Scottapotamas/stm32-camera/Firmware/stm32-camera/Src/app_hal/hal_gpio_types.h

/**
 * @file      hal_gpio_types.h
 *
 * @brief     Type declarations for GPIO use.
 *
 * @author    Marco Hess <marcoh@applidyne.com.au>
 *
 * @copyright (c) 2017 Applidyne Pty. Ltd. - All rights reserved.
*/

#ifndef HAL_GPIO_TYPES_H
#define HAL_GPIO_TYPES_H

#ifdef __cplusplus
extern "C" {
#endif

#include <stdbool.h>

#include "global.h"

/** Readability macros to remind us which is a HIGH level or LOW level */
#define GPIO_HIGH       true
#define GPIO_LOW        false

/** Map the pin number into a bit mask */
#define HAL_GPIO_PIN_MASK( pin_nr )   (1UL << ( pin_nr ))

/* ----- Types ------------------------------------------------------------- */

/** Operational mode for pins */

typedef enum
{
    MODE_INPUT = 0, /* Normal input */
    MODE_INPUT_PU, /* Input with PU */
    MODE_ANALOG,    /* Analog Mode  */
    MODE_OUT_PP,    /* Push-Pull Output */
    MODE_OUT_OD     /* Open drain Output */
} HalGpioMode_t;

/** Port Number */
typedef enum
{
    PORT_A = (0),
    PORT_B = (1),
    PORT_C = (2),
    PORT_D = (3),
    PORT_E = (4),
    PORT_F = (5),
    PORT_G = (6),
    PORT_H = (7),
	I2C_PLACEHOLDER
} HalGpioPortNr_t;

/** Pin Numbers */
typedef enum
{
    PIN_0,
    PIN_1,
    PIN_2,
    PIN_3,
    PIN_4,
    PIN_5,
    PIN_6,
    PIN_7,
    PIN_8,
    PIN_9,
    PIN_10,
    PIN_11,
    PIN_12,
    PIN_13,
    PIN_14,
    PIN_15,
} HalGpioPinNr_t;

typedef struct
{
    unsigned mode       : 3;      /* GPIO Mode (Input, Output Push Pull, etc. ) TODO work out analog pin mode requiring more bits*/
    unsigned port       : 4;      /* GPIO Port */
    unsigned pin        : 5;      /* Pin Number within port or i2C device */
    unsigned initial    : 1;      /* Initialisation level for outputs */
} HalGpioDef_t;

/* ----- End ---------------------------------------------------------------- */

#ifdef __cplusplus
}
#endif

#endif /* HAL_GPIO_TYPES_H */
