Scottapotamas/stm32-camera/Firmware/stm32-camera/Src/app_hal/hal_uart.h

/**
 * @file      hal_uart.h
 *
 * @brief     Low level interface to the UARTs.
 *
 * @author    Marco Hess <marcoh@applidyne.com.au>
 *
 * @copyright (c) 2017 Applidyne Pty. Ltd. - All rights reserved.
*/

#ifndef HAL_UART_H
#define HAL_UART_H

#ifdef __cplusplus
extern "C" {
#endif

/* ----- System Includes ---------------------------------------------------- */

#include <stdint.h>
#include <stdbool.h>

/* ----- Local Includes ----------------------------------------------------- */

#include "global.h"

/* ----- Types ------------------------------------------------------------- */

typedef enum
{
    HAL_UART_PORT_MAIN,
    HAL_UART_NUM_PORTS
} HalUartPort_t;

typedef void (*HalUartRxCallback_t)( HalUartPort_t port, uint8_t c );

/* -------------------------------------------------------------------------- */
/* --- UART INTERFACE                                                     --- */
/* -------------------------------------------------------------------------- */

/** Initialise the UARTs */

PUBLIC void
hal_uart_init( HalUartPort_t port );

/* -------------------------------------------------------------------------- */

/* Reset the UART (for after clock speed change) */

PUBLIC void
hal_uart_reinit( HalUartPort_t port );

/* -------------------------------------------------------------------------- */

/** Activate the UART peripheral */

PUBLIC void
hal_uart_activate( HalUartPort_t port );

/* -------------------------------------------------------------------------- */

/** Deactivate the UART peripheral */

PUBLIC void
hal_uart_deactivate( HalUartPort_t port );

/* -------------------------------------------------------------------------- */

/** Configure the UART baudrate */

PUBLIC void
hal_uart_baudrate( HalUartPort_t port, uint32_t baudrate );

/* -------------------------------------------------------------------------- */

/* Non-blocking send for a single character to the UART tx FIFO queue.
 * Returns true when successful. false when queue was full.
 */

PUBLIC bool
hal_uart_put( HalUartPort_t port, uint8_t c );

/* -------------------------------------------------------------------------- */

/** Wait until FIFO cleared. */

PUBLIC void
hal_uart_flush( HalUartPort_t port );

/* -------------------------------------------------------------------------- */

/* Blocking send for a single character to the UART tx FIFO queue.
 * Can still return unsuccessfully when timing out.
 * Returns true when successful. false when queue was full.
 */

PUBLIC bool
hal_uart_put_blocking( HalUartPort_t port, uint8_t c );

/* -------------------------------------------------------------------------- */

/* Non-blocking send for a number of characters to the UART tx FIFO queue.
 * Returns true when successful. false when queue was full.
 */

PUBLIC uint32_t
hal_uart_write( HalUartPort_t port, const uint8_t * data, uint32_t length );

/* -------------------------------------------------------------------------- */

/* Register a receive handler.
 * Called directly from UART ISR. When this is used, there is no buffering
 * available and the hal_uart_get is no longer functional.
 */

PUBLIC void
hal_uart_set_rx_handler( HalUartPort_t port, HalUartRxCallback_t rxFunc );

/* -------------------------------------------------------------------------- */

/* Returns number of available characters in the RX FIFO queue. */

PUBLIC uint32_t
hal_uart_rx_data_available( HalUartPort_t port );

/* -------------------------------------------------------------------------- */

/* Retrieve a single byte from the rx FIFO queue.
 * Returns 0 when no data is available or when rx callback is in use.
 */

PUBLIC uint8_t
hal_uart_rx_get( HalUartPort_t port );

/* -------------------------------------------------------------------------- */

/* Retrieve a number of bytes from the rx FIFO queue up to
 * buffer length. Returns the number of bytes actually read.
 */

PUBLIC uint32_t
hal_uart_read( HalUartPort_t port, uint8_t * buffer, uint32_t bufferlen );

/* -------------------------------------------------------------------------- */

/* Blocking printf to the UART.
 * To be used within assert and fault handlers to print fault
 * information.
 */

PUBLIC void
hal_uart_printf_direct( HalUartPort_t port, const char * format, ... );

/* ----- End ---------------------------------------------------------------- */

#ifdef __cplusplus
}
#endif

#endif /* HAL_UART_H */
