Scottapotamas/stm32-camera/Firmware/stm32-camera/Src/app_state_machines/app_events.h

/**
 * @file    app_events.h
 *
 * @brief   Application Level Custom Event Structures.
 *
 * @author  Marco Hess <marcoh@applidyne.com.au>
 *
 * @copyright (c) 2013-2015 Applidyne Pty. Ltd. - All rights reserved.
 */

#ifndef APP_EVENTS_H
#define APP_EVENTS_H

#ifdef __cplusplus
extern "C" {
#endif

/* ----- System Includes ---------------------------------------------------- */

#include <stdint.h>
#include <stdbool.h>
#include <time.h>

/* ----- Local Includes ----------------------------------------------------- */

#include "global.h"
#include "app_config.h"
#include "state_task.h"
#include "state_event.h"
#include "button.h"
#include "hal_i2c.h"
#include "auxiliary.h"
#include "hal_uart.h"
#include "ff.h"
#include "auxiliary.h"
#include "log.h"

/* -------------------------------------------------------------------------- */

/** Internal report of button event */
typedef struct ButtonEvent__
{
    StateEvent        super;             /**< Encapsulated event reference */
    ButtonId_t        id;                /**< ID number of button event */
    ButtonPressType_t press_type;        /**< Type of button event */
} ButtonEvent;

/** Report detected button presses */
typedef struct ButtonPressedEvent__
{
    StateEvent    super;             /**< Encapsulated event reference */
    ButtonId_t    id;                /**< ID number of button event */
} ButtonPressedEvent;

/* -------------------------------------------------------------------------- */

/** Camera Capture Cmd Event Structures */
typedef struct CameraCaptureEvent__
{
    StateEvent          super;          /**< Encapsulated event reference */
    uint16_t            trigger_delay_ms;   /**< Time in ms to wait before taking picture */
} CameraCaptureEvent;

/* -------------------------------------------------------------------------- */

/** Camera Save Event Structures */
typedef struct CameraSaveEvent__
{
    StateEvent      super;              /**< Encapsulated event reference */
    uint8_t         percent_saved;      /**< Percentage of image saved */
} CameraSaveEvent;

/* -------------------------------------------------------------------------- */

/** Report changes in auxillary mode */
typedef struct AuxiliaryModeEvent__
{
    StateEvent       super;          /**< Encapsulated event reference */
    AuxiliaryPort_t  port;           /**< Aux port for mode switch */
    AuxiliaryMode_t  mode;           /**< Aux mode to switch to */
} AuxiliaryModeEvent;

/* -------------------------------------------------------------------------- */

/** Log Buffer Event - Generated when a log message occurs */
typedef struct LogBufferEvent__
{
    StateEvent      super;              /**< Encapsulated event reference */
    LOG_LEVEL       level;              /**< Log Message Level */
    uint32_t        used;               /**< Log buffer space used */
    uint32_t        percent;            /**< Log Buffer percentage used */
} LogBufferEvent;

/* -------------------------------------------------------------------------- */

/** Report changes in terminal mode */
typedef struct TerminalModeEvent__
{
    StateEvent       super;          /**< Encapsulated event reference */
    HalUartPort_t	 port;           /**< terminal port for mode switch */
    //TODO use a mode object here to act as baud rate allowing for event calls on baud change.
} TerminalModeEvent;

/* -------------------------------------------------------------------------- */

typedef struct TerminalCharEvent__
{
    StateEvent    super;
    uint8_t       ch;
} TerminalCharEvent;

/* -------------------------------------------------------------------------- */

/** Report detected button presses */
typedef struct KeyboardEvent__
{
    StateEvent super;             /**< Encapsulated event reference */
    char       key;
} KeyboardEvent;

/* -------------------------------------------------------------------------- */

/** File System Status Event Structures */
typedef struct FileSystemRequestEvent__
{
    StateEvent super;             /**< Encapsulated event reference */
    StateTask  *task;             /**< Task pointer making the request.
                                       Should not be more than 1 per task */
} FileSystemRequestEvent;

/* -------------------------------------------------------------------------- */

/** File System Status Event Structures */
typedef struct FileSystemStatusEvent__
{
    StateEvent super;             /**< Encapsulated event reference */
    FRESULT    f_result;          /**< FatFS FRESULT of mount/unmount */
    uint8_t    number_of_mounts;  /**< Number of tasks with an open mount */
    uint32_t   space_total_KiB;   /**< Total KiB for disk */
    uint32_t   space_free_KiB;    /**< Free KiB on disk */
} FileSystemStatusEvent;

/* ----- End ---------------------------------------------------------------- */

#ifdef __cplusplus
}
#endif

#endif /* APP_EVENTS_H */
