Scottapotamas/stm32-camera/Firmware/stm32-camera/Src/app_state_machines/app_task_terminal.c

/**
 * @file    app_task_terminal.c
 *
 * @ingroup tasks
 *
 * @brief   blah
 *
 *
 * @copyright (c) 2015 Applidyne Pty. Ltd. - All rights reserved.
 */

/* ----- System Includes ---------------------------------------------------- */

#include <ctype.h>
#include <string.h>
#include <event_subscribe.h>

/* ----- Local Includes ----------------------------------------------------- */

#include "global.h"
#include "qassert.h"
#include "app_config.h"
#include "app_tasks.h"
#include "app_task_ids.h"
#include "app_times.h"
#include "app_signals.h"
#include "app_events.h"
#include "app_version.h"
#include "hal_systick.h"

#include "app_task_terminal.h"
#include "app_task_terminal_private.h"
#include "commands.h"
#include "log.h"
#include "config.h"

/* -------------------------------------------------------------------------- */

//DEFINE_THIS_FILE; /* Used for ASSERT checks to define __FILE__ only once */

/* ----------------------- Public Functions --------------------------------- */

PUBLIC StateTask *
appTaskTerminalCreate( AppTaskTerminal   *me,
                        StateEvent         *eventQueueData[ ],
                        const uint8_t      eventQueueSize,
						HalUartPort_t      instance )
{
    /* Clear all task data */
    memset( me, 0, sizeof(AppTaskTerminal) );

    /* Initialise State Machine structures */
    AppTaskTerminalConstructor( me );

    /* Which uart are we talking about */
    me->instance = instance;

    /* Initialise State Machine Task */
    return stateTaskCreate( (StateTask*)me,
                            eventQueueData,
                            eventQueueSize,
                            0,
                            0 );
}

/* ----- Private Functions -------------------------------------------------- */

/* State Machine Construction */
PRIVATE void AppTaskTerminalConstructor( AppTaskTerminal *me )
{
    stateTaskCtor( &me->super, (State)&AppTaskTerminal_initial );
}

/* -------------------------------------------------------------------------- */

/*  State Machine Initial State */
PRIVATE void AppTaskTerminal_initial( AppTaskTerminal *me,
                                       const StateEvent *e __attribute__((__unused__)) )
{
    eventSubscribe( (StateTask*)me, TERMINAL_MODE_SIGNAL );
    STATE_INIT( &AppTaskTerminal_main );
}

/* -------------------------------------------------------------------------- */

/* State Machine Initial State */
PRIVATE STATE
AppTaskTerminal_main( AppTaskTerminal *me,
                       const StateEvent *e )
{
    switch( e->signal )
    {
        case STATE_ENTRY_SIGNAL:

        	cmd_init( &me->monitor, commands );

        	//configure the uart
            hal_uart_init( me->instance );
            hal_uart_baudrate( me->instance, config_terminal_baudrate( me->instance ) );
            hal_uart_set_rx_handler( me->instance, AppTaskTerminal_rx_callback );

            //configure the terminal interface
            cmd_set_output_put( &me->monitor, AppTaskTerminal_tx_put );
            cmd_set_output_flush( &me->monitor,  AppTaskTerminal_tx_flush );
            cmd_set_echo( &me->monitor, true );

            //Logging system can use this monitor as the output.
            command_log_set_mask( &me->monitor, 0xFFFF, LOG_MASK_ALL );

            //print board info to terminal
            cmd_printf( &me->monitor,
                        "\r\n*** %s - %s (%s) %s ***\r\n\r\n",
                        ProgramName,
                        ProgramBuildInfo,
                        ProgramBuildDate,
                        ProgramBuildType );
            cmd_input_func( &me->monitor, '\r' );

            return 0;

        case TERMINAL_INPUT_CHAR_SIGNAL:
            cmd_input_func( &me->monitor, ((TerminalCharEvent*)e)->ch );
            //no break

        case STATE_STEP1_SIGNAL:
            me->monitor.flags.cmdDone = cmd_main_loop( &me->monitor );
            if( !me->monitor.flags.cmdDone )
            {
                /* Repeat until done */
                stateTaskPostReservedEvent( STATE_STEP1_SIGNAL );
            }
            return 0;
    }
    return (STATE)hsmTop;
}

/* -------------------------------------------------------------------------- */

//TODO write state machine to handle changing baud rate

/* ----- Callback Helper Functions ------------------------------------------ */

PRIVATE bool
AppTaskTerminal_tx_put( uint8_t c )
{
    return hal_uart_put( HAL_UART_PORT_MAIN, c );
}

/* -------------------------------------------------------------------------- */

PRIVATE void
AppTaskTerminal_tx_flush( void )
{
    hal_uart_flush( HAL_UART_PORT_MAIN );
}

/* -------------------------------------------------------------------------- */

/* Simple callback for received characters */
PRIVATE void
AppTaskTerminal_rx_callback( HalUartPort_t port, uint8_t c )
{
    if( port == HAL_UART_PORT_MAIN )
    {
        TerminalCharEvent *e = EVENT_NEW( TerminalCharEvent, TERMINAL_INPUT_CHAR_SIGNAL );

        // Failure of EVENT_NEW allocate results in a corrupted input message
        if( e )
        {
            e->ch = c;
            if( port == HAL_UART_PORT_MAIN )
            {
                stateTaskPostFIFO( app_task_by_id( TASK_TERMINAL ),
                                   (StateEvent*)e );
            }

        }
    }
    else
    {
    	//handle other uart ports here if future boards need them
    }
}

/* ----- End ---------------------------------------------------------------- */
