Scottapotamas/stm32-camera/Firmware/stm32-camera/Src/app_hal/hal_solenoid.c

/**
 * @file      hal_solenoid.c
 *
 * @brief     Low level interface to the solenoid drive "H-Bridge".
 *
*/

/* ----- System Includes ---------------------------------------------------- */

/* ----- Local Includes ----------------------------------------------------- */

#include "hal_solenoid.h"
#include "stm32f4xx_hal.h"


PUBLIC void
hal_solenoid_init( )
{
    //TODO init solenoid drive
}

/* -------------------------------------------------------------------------- */

PUBLIC void
hal_solenoid_off( )
{
    //write all pins as 'off'
    HAL_GPIO_WritePin(GPIOE, GPIO_PIN_7|GPIO_PIN_8|GPIO_PIN_9|GPIO_PIN_10, GPIO_PIN_RESET);
    HAL_GPIO_WritePin(GPIOE, GPIO_PIN_11|GPIO_PIN_12|GPIO_PIN_13|GPIO_PIN_14, GPIO_PIN_RESET);

    //turn all pins to an input or analog "passive" state for "off"
    GPIO_InitTypeDef GPIO_InitStruct;

    GPIO_InitStruct.Pin = GPIO_PIN_7|GPIO_PIN_8|GPIO_PIN_9|GPIO_PIN_10|
                          GPIO_PIN_11|GPIO_PIN_12|GPIO_PIN_13|GPIO_PIN_14;
    GPIO_InitStruct.Mode = GPIO_MODE_ANALOG;    //save power by setting as analog
    GPIO_InitStruct.Pull = GPIO_NOPULL;
    GPIO_InitStruct.Speed = GPIO_SPEED_FREQ_LOW;

    HAL_GPIO_Init(GPIOE, &GPIO_InitStruct);
}

/* -------------------------------------------------------------------------- */

PUBLIC void
hal_solenoid_activate( bool polarity )
{
    //port setup for pins
    GPIO_InitTypeDef GPIO_InitStruct;

    GPIO_InitStruct.Pin = GPIO_PIN_7|GPIO_PIN_8|GPIO_PIN_9|GPIO_PIN_10|
                          GPIO_PIN_11|GPIO_PIN_12|GPIO_PIN_13|GPIO_PIN_14;
    GPIO_InitStruct.Mode = GPIO_MODE_OUTPUT_PP;    //configure push pull
    GPIO_InitStruct.Pull = GPIO_NOPULL;
    GPIO_InitStruct.Speed = GPIO_SPEED_FREQ_LOW;

    HAL_GPIO_Init(GPIOE, &GPIO_InitStruct);

    //write all pins as 'off'
    HAL_GPIO_WritePin(GPIOE, GPIO_PIN_7|GPIO_PIN_8|GPIO_PIN_9|GPIO_PIN_10, GPIO_PIN_RESET);
    HAL_GPIO_WritePin(GPIOE, GPIO_PIN_11|GPIO_PIN_12|GPIO_PIN_13|GPIO_PIN_14, GPIO_PIN_RESET);

    hal_delay_ms(1);    //todo don't delay in solenoid like this

    //half the port has polarity, the other half has !polarity to set them half on and half off
    HAL_GPIO_WritePin(GPIOE, GPIO_PIN_7|GPIO_PIN_8|GPIO_PIN_9|GPIO_PIN_10, polarity);
    HAL_GPIO_WritePin(GPIOE, GPIO_PIN_11|GPIO_PIN_12|GPIO_PIN_13|GPIO_PIN_14, !polarity);

}


/* ----- End ---------------------------------------------------------------- */
