Scottapotamas/stm32-camera/Firmware/stm32-camera/Src/app_hal/hal_uuid.h

/**
 * @file      hal_uuid.c
 *
 * @brief     A simple header for reading the STM32 device UUID
 *            Tested with STM32F4 and STM32F0 families
 *
 * @author    Uli Koehler
 *            Published on http://techoverflow.net
 *
 * @licence   Licensed under CC0 (public domain):
 *            https://creativecommons.org/publicdomain/zero/1.0/
 */

#ifndef HAL_UUID_H
#define HAL_UUID_H

#include <stdint.h>

/**
 * The STM32 factory-programmed UUID memory.
 * Three values of 32 bits each starting at this address
 * Use like this: STM32_UUID[0], STM32_UUID[1], STM32_UUID[2]
 */
#define HAL_UUID ((uint32_t *)0x1FFF7A10)

#endif /* HAL_UUID_H */
 
