Scottapotamas/stm32-camera/Firmware/stm32-camera/Src/app_state_machines/app_background.c

/**
 * @file      app_background.c
 *
 * @brief     Application main loop background processes
 *
 * @author    Marco Hess <marcoh@applidyne.com.au>
 *
 * @copyright (c) 2017 Applidyne Pty. Ltd. - All rights reserved.
 */

/* ----- System Includes ---------------------------------------------------- */


/* ----- Local Includes ----------------------------------------------------- */

#include "app_background.h"
#include "event_subscribe.h"
#include "app_signals.h"
#include "button.h"
#include "hal_button.h"
#include "timer.h"

/* -------------------------------------------------------------------------- */

PRIVATE timer_t button_timer = 0;

/* -------------------------------------------------------------------------- */

PUBLIC void
app_background_init( void )
{
    timerStart( &button_timer, 50 );

}

/* -------------------------------------------------------------------------- */

PUBLIC void
app_background( void )
{
    if( timerIsExpired( &button_timer ) )
    {
        timerStart( &button_timer, 50 );
    }

    /* Scan buttons */
    button_process();

}

/* ----- End ---------------------------------------------------------------- */
