Scottapotamas/stm32-camera/Firmware/stm32-camera/Src/app_state_machines/app_background.h

/**
 * @file      app_background.h
 *
 * @brief     Application main loop background processes
 *
 * @author    Marco Hess <marcoh@applidyne.com.au>
 *
 * @copyright (c) 2017 Applidyne Pty. Ltd. - All rights reserved.
 */

#ifndef APP_BACKGROUND_H
#define APP_BACKGROUND_H

#ifdef __cplusplus
extern "C" {
#endif

/* ----- System Includes ---------------------------------------------------- */

/* ----- Local Includes ----------------------------------------------------- */

#include "global.h"

/* ----- Defines ------------------------------------------------------------ */

/* ----- Public Functions --------------------------------------------------- */

/** Startup initialisation for background processes in the main loop */

PUBLIC void
app_background_init( void );

/* -------------------------------------------------------------------------- */

/** Background processes that are handled in the main loop */

PUBLIC void
app_background( void );

/* ----- End ------------------------------~--------------------------------- */

#ifdef    __cplusplus
}
#endif
#endif /* APP_BACKGROUND_H */
