Scottapotamas/stm32-camera/Firmware/stm32-camera/Src/app_utility/eunity.c

/* =========================================================================
    eUnity Project - A Test Framework for C
    Copyright (c) 2007-14 Mike Karlesky, Mark VanderVoord, Greg Williams
    [Released under MIT License. Please refer to license.txt for details]
============================================================================ */

#include "eunity.h"
#include <stddef.h>

/* If omitted from header, declare overrideable prototypes here so they're ready for use */
#ifdef EUNITY_OMIT_OUTPUT_CHAR_HEADER_DECLARATION
void EUNITY_OUTPUT_CHAR(int);
#endif

/* Helpful macros for us to use here */
#define EUNITY_FAIL_AND_BAIL   { eUnity.CurrentTestFailed  = 1; longjmp(eUnity.AbortFrame, 1); }
#define EUNITY_IGNORE_AND_BAIL { eUnity.CurrentTestIgnored = 1; longjmp(eUnity.AbortFrame, 1); }

/* return prematurely if we are already in failure or ignore state */
#define EUNITY_SKIP_EXECUTION  { if ((eUnity.CurrentTestFailed != 0) || (eUnity.CurrentTestIgnored != 0)) {return;} }

struct _eUnity eUnity;

static const char eUnityStrOk[]                     = "OK";
static const char eUnityStrPass[]                   = "PASS";
static const char eUnityStrFail[]                   = "FAIL";
static const char eUnityStrIgnore[]                 = "IGNORE";
static const char eUnityStrNull[]                   = "NULL";
static const char eUnityStrSpacer[]                 = ". ";
static const char eUnityStrExpected[]               = " Expected ";
static const char eUnityStrWas[]                    = " Was ";
static const char eUnityStrElement[]                = " Element ";
static const char eUnityStrByte[]                   = " Byte ";
static const char eUnityStrMemory[]                 = " Memory Mismatch.";
static const char eUnityStrDelta[]                  = " Values Not Within Delta ";
static const char eUnityStrPointless[]              = " You Asked Me To Compare Nothing, Which Was Pointless.";
static const char eUnityStrNullPointerForExpected[] = " Expected pointer to be NULL";
static const char eUnityStrNullPointerForActual[]   = " Actual pointer was NULL";
static const char eUnityStrNot[]                    = "Not ";
static const char eUnityStrInf[]                    = "Infinity";
static const char eUnityStrNegInf[]                 = "Negative Infinity";
static const char eUnityStrNaN[]                    = "NaN";
static const char eUnityStrDet[]                    = "Determinate";
static const char eUnityStrInvalidFloatTrait[]      = "Invalid Float Trait";
const char eUnityStrErrFloat[]                      = "Unity Floating Point Disabled";
const char eUnityStrErrDouble[]                     = "Unity Double Precision Disabled";
const char eUnityStrErr64[]                         = "Unity 64-bit Support Disabled";
static const char eUnityStrBreaker[]                = "-----------------------";
static const char eUnityStrResultsTests[]           = " Tests ";
static const char eUnityStrResultsFailures[]        = " Failures ";
static const char eUnityStrResultsIgnored[]         = " Ignored ";
static const char eUnityStrDetail1Name[]            = EUNITY_DETAIL1_NAME " ";
static const char eUnityStrDetail2Name[]            = " " EUNITY_DETAIL2_NAME " ";

#ifdef EUNITY_FLOAT_NEEDS_ZERO
/* Dividing by these constants produces +/- infinity.
 * The rationale is given in eUnityAssertFloatIsInf's body. */
static const _UF f_zero = 0.0f;
#endif

/* compiler-generic print formatting masks */
static const _U_UINT eUnitySizeMask[] =
{
    255u,         /* 0xFF */
    65535u,       /* 0xFFFF */
    65535u,
    4294967295u,  /* 0xFFFFFFFF */
    4294967295u,
    4294967295u,
    4294967295u
#ifdef EUNITY_SUPPORT_64
    ,0xFFFFFFFFFFFFFFFF
#endif
};

/*-----------------------------------------------
 * Pretty Printers & Test Result Output Handlers
 *-----------------------------------------------*/

void eUnityPrint(const char* string)
{
    const char* pch = string;

    if (pch != NULL)
    {
        while (*pch)
        {
            /* printable characters plus CR & LF are printed */
            if ((*pch <= 126) && (*pch >= 32))
            {
                EUNITY_OUTPUT_CHAR(*pch);
            }
            /* write escaped carriage returns */
            else if (*pch == 13)
            {
                EUNITY_OUTPUT_CHAR('\\');
                EUNITY_OUTPUT_CHAR('r');
            }
            /* write escaped line feeds */
            else if (*pch == 10)
            {
                EUNITY_OUTPUT_CHAR('\\');
                EUNITY_OUTPUT_CHAR('n');
            }
            /* unprintable characters are shown as codes */
            else
            {
                EUNITY_OUTPUT_CHAR('\\');
                eUnityPrintNumberHex((_U_UINT)*pch, 2);
            }
            pch++;
        }
    }
}

void eUnityPrintLen(const char* string, const _UU32 length);
void eUnityPrintLen(const char* string, const _UU32 length)
{
    const char* pch = string;

    if (pch != NULL)
    {
        while (*pch && (_UU32)(pch - string) < length)
        {
            /* printable characters plus CR & LF are printed */
            if ((*pch <= 126) && (*pch >= 32))
            {
                EUNITY_OUTPUT_CHAR(*pch);
            }
            /* write escaped carriage returns */
            else if (*pch == 13)
            {
                EUNITY_OUTPUT_CHAR('\\');
                EUNITY_OUTPUT_CHAR('r');
            }
            /* write escaped line feeds */
            else if (*pch == 10)
            {
                EUNITY_OUTPUT_CHAR('\\');
                EUNITY_OUTPUT_CHAR('n');
            }
            /* unprintable characters are shown as codes */
            else
            {
                EUNITY_OUTPUT_CHAR('\\');
                eUnityPrintNumberHex((_U_UINT)*pch, 2);
            }
            pch++;
        }
    }
}

/*-----------------------------------------------*/
void eUnityPrintNumberByStyle(const _U_SINT number, const EUNITY_DISPLAY_STYLE_T style)
{
    if ((style & EUNITY_DISPLAY_RANGE_INT) == EUNITY_DISPLAY_RANGE_INT)
    {
        eUnityPrintNumber(number);
    }
    else if ((style & EUNITY_DISPLAY_RANGE_UINT) == EUNITY_DISPLAY_RANGE_UINT)
    {
        eUnityPrintNumberUnsigned(  (_U_UINT)number  &  eUnitySizeMask[((_U_UINT)style & (_U_UINT)0x0F) - 1]  );
    }
    else
    {
        eUnityPrintNumberHex((_U_UINT)number, (char)((style & 0x000F) << 1));
    }
}

/*-----------------------------------------------*/
void eUnityPrintNumber(const _U_SINT number_to_print)
{
    _U_UINT number = (_U_UINT)number_to_print;

    if (number_to_print < 0)
    {
        /* A negative number, including MIN negative */
        EUNITY_OUTPUT_CHAR('-');
        number = (_U_UINT)(-number_to_print);
    }
    eUnityPrintNumberUnsigned(number);
}

/*-----------------------------------------------
 * basically do an itoa using as little ram as possible */
void eUnityPrintNumberUnsigned(const _U_UINT number)
{
    _U_UINT divisor = 1;

    /* figure out initial divisor */
    while (number / divisor > 9)
    {
        divisor *= 10;
    }

    /* now mod and print, then divide divisor */
    do
    {
        EUNITY_OUTPUT_CHAR((char)('0' + (number / divisor % 10)));
        divisor /= 10;
    }
    while (divisor > 0);
}

/*-----------------------------------------------*/
void eUnityPrintNumberHex(const _U_UINT number, const char nibbles_to_print)
{
    _U_UINT nibble;
    char nibbles = nibbles_to_print;
    EUNITY_OUTPUT_CHAR('0');
    EUNITY_OUTPUT_CHAR('x');

    while (nibbles > 0)
    {
        nibble = (number >> (--nibbles << 2)) & 0x0000000F;
        if (nibble <= 9)
        {
            EUNITY_OUTPUT_CHAR((char)('0' + nibble));
        }
        else
        {
            EUNITY_OUTPUT_CHAR((char)('A' - 10 + nibble));
        }
    }
}

/*-----------------------------------------------*/
void eUnityPrintMask(const _U_UINT mask, const _U_UINT number)
{
    _U_UINT current_bit = (_U_UINT)1 << (EUNITY_INT_WIDTH - 1);
    _US32 i;

    for (i = 0; i < EUNITY_INT_WIDTH; i++)
    {
        if (current_bit & mask)
        {
            if (current_bit & number)
            {
                EUNITY_OUTPUT_CHAR('1');
            }
            else
            {
                EUNITY_OUTPUT_CHAR('0');
            }
        }
        else
        {
            EUNITY_OUTPUT_CHAR('X');
        }
        current_bit = current_bit >> 1;
    }
}

/*-----------------------------------------------*/
#ifdef EUNITY_FLOAT_VERBOSE
#include <stdio.h>

#ifndef EUNITY_VERBOSE_NUMBER_MAX_LENGTH
# ifdef EUNITY_DOUBLE_VERBOSE
#  define EUNITY_VERBOSE_NUMBER_MAX_LENGTH 317
# else
#  define EUNITY_VERBOSE_NUMBER_MAX_LENGTH 47
# endif
#endif

void eUnityPrintFloat(_UF number)
{
    char TempBuffer[EUNITY_VERBOSE_NUMBER_MAX_LENGTH + 1];
    snprintf(TempBuffer, sizeof(TempBuffer), "%.6f", number);
    eUnityPrint(TempBuffer);
}
#endif

/*-----------------------------------------------*/

void eUnityPrintFail(void);
void eUnityPrintFail(void)
{
    eUnityPrint(eUnityStrFail);
}

void eUnityPrintOk(void);
void eUnityPrintOk(void)
{
    eUnityPrint(eUnityStrOk);
}

/*-----------------------------------------------*/
static void eUnityTestResultsBegin(const char* file, const EUNITY_LINE_TYPE line);
static void eUnityTestResultsBegin(const char* file, const EUNITY_LINE_TYPE line)
{
#ifndef EUNITY_FIXTURES
    eUnityPrint(file);
    EUNITY_OUTPUT_CHAR(':');
    eUnityPrintNumber((_U_SINT)line);
    EUNITY_OUTPUT_CHAR(':');
    eUnityPrint(eUnity.CurrentTestName);
    EUNITY_OUTPUT_CHAR(':');
#else
    EUNITY_UNUSED(file);
    EUNITY_UNUSED(line);
#endif
}

/*-----------------------------------------------*/
static void eUnityTestResultsFailBegin(const EUNITY_LINE_TYPE line);
static void eUnityTestResultsFailBegin(const EUNITY_LINE_TYPE line)
{
#ifndef EUNITY_FIXTURES
    eUnityTestResultsBegin(eUnity.TestFile, line);
#else
    EUNITY_UNUSED(line);
#endif
    eUnityPrint(eUnityStrFail);
    EUNITY_OUTPUT_CHAR(':');
}

/*-----------------------------------------------*/
void eUnityConcludeTest(void)
{
    if (eUnity.CurrentTestIgnored)
    {
        eUnity.TestIgnores++;
    }
    else if (!eUnity.CurrentTestFailed)
    {
        eUnityTestResultsBegin(eUnity.TestFile, eUnity.CurrentTestLineNumber);
        eUnityPrint(eUnityStrPass);
    }
    else
    {
        eUnity.TestFailures++;
    }

    eUnity.CurrentTestFailed = 0;
    eUnity.CurrentTestIgnored = 0;
    EUNITY_PRINT_EOL();
    EUNITY_FLUSH_CALL();
}

/*-----------------------------------------------*/
static void eUnityAddMsgIfSpecified(const char* msg);
static void eUnityAddMsgIfSpecified(const char* msg)
{
    if (msg)
    {
        eUnityPrint(eUnityStrSpacer);
#ifndef EUNITY_EXCLUDE_DETAILS
        if (eUnity.CurrentDetail1)
        {
            eUnityPrint(eUnityStrDetail1Name);
            eUnityPrint(eUnity.CurrentDetail1);
            if (eUnity.CurrentDetail2)
            {
                eUnityPrint(eUnityStrDetail2Name);
                eUnityPrint(eUnity.CurrentDetail2);
            }
            eUnityPrint(eUnityStrSpacer);
        }
#endif
        eUnityPrint(msg);
    }
}

/*-----------------------------------------------*/
static void eUnityPrintExpectedAndActualStrings(const char* expected, const char* actual);
static void eUnityPrintExpectedAndActualStrings(const char* expected, const char* actual)
{
    eUnityPrint(eUnityStrExpected);
    if (expected != NULL)
    {
        EUNITY_OUTPUT_CHAR('\'');
        eUnityPrint(expected);
        EUNITY_OUTPUT_CHAR('\'');
    }
    else
    {
      eUnityPrint(eUnityStrNull);
    }
    eUnityPrint(eUnityStrWas);
    if (actual != NULL)
    {
        EUNITY_OUTPUT_CHAR('\'');
        eUnityPrint(actual);
        EUNITY_OUTPUT_CHAR('\'');
    }
    else
    {
      eUnityPrint(eUnityStrNull);
    }
}

/*-----------------------------------------------*/
static void eUnityPrintExpectedAndActualStringsLen(const char* expected, const char* actual, const _UU32 length)
{
    eUnityPrint(eUnityStrExpected);
    if (expected != NULL)
    {
        EUNITY_OUTPUT_CHAR('\'');
        eUnityPrintLen(expected, length);
        EUNITY_OUTPUT_CHAR('\'');
    }
    else
    {
      eUnityPrint(eUnityStrNull);
    }
    eUnityPrint(eUnityStrWas);
    if (actual != NULL)
    {
        EUNITY_OUTPUT_CHAR('\'');
        eUnityPrintLen(actual, length);
        EUNITY_OUTPUT_CHAR('\'');
    }
    else
    {
      eUnityPrint(eUnityStrNull);
    }
}



/*-----------------------------------------------
 * Assertion & Control Helpers
 *-----------------------------------------------*/

static int eUnityCheckArraysForNull(EUNITY_INTERNAL_PTR expected, EUNITY_INTERNAL_PTR actual, const EUNITY_LINE_TYPE lineNumber, const char* msg)
{
    /* return true if they are both NULL */
    if ((expected == NULL) && (actual == NULL))
        return 1;

    /* throw error if just expected is NULL */
    if (expected == NULL)
    {
        eUnityTestResultsFailBegin(lineNumber);
        eUnityPrint(eUnityStrNullPointerForExpected);
        eUnityAddMsgIfSpecified(msg);
        EUNITY_FAIL_AND_BAIL;
    }

    /* throw error if just actual is NULL */
    if (actual == NULL)
    {
        eUnityTestResultsFailBegin(lineNumber);
        eUnityPrint(eUnityStrNullPointerForActual);
        eUnityAddMsgIfSpecified(msg);
        EUNITY_FAIL_AND_BAIL;
    }

    /* return false if neither is NULL */
    return 0;
}

/*-----------------------------------------------
 * Assertion Functions
 *-----------------------------------------------*/

void eUnityAssertBits(const _U_SINT mask,
                     const _U_SINT expected,
                     const _U_SINT actual,
                     const char* msg,
                     const EUNITY_LINE_TYPE lineNumber)
{
    EUNITY_SKIP_EXECUTION;

    if ((mask & expected) != (mask & actual))
    {
        eUnityTestResultsFailBegin(lineNumber);
        eUnityPrint(eUnityStrExpected);
        eUnityPrintMask((_U_UINT)mask, (_U_UINT)expected);
        eUnityPrint(eUnityStrWas);
        eUnityPrintMask((_U_UINT)mask, (_U_UINT)actual);
        eUnityAddMsgIfSpecified(msg);
        EUNITY_FAIL_AND_BAIL;
    }
}

/*-----------------------------------------------*/
void eUnityAssertEqualNumber(const _U_SINT expected,
                            const _U_SINT actual,
                            const char* msg,
                            const EUNITY_LINE_TYPE lineNumber,
                            const EUNITY_DISPLAY_STYLE_T style)
{
    EUNITY_SKIP_EXECUTION;

    if (expected != actual)
    {
        eUnityTestResultsFailBegin(lineNumber);
        eUnityPrint(eUnityStrExpected);
        eUnityPrintNumberByStyle(expected, style);
        eUnityPrint(eUnityStrWas);
        eUnityPrintNumberByStyle(actual, style);
        eUnityAddMsgIfSpecified(msg);
        EUNITY_FAIL_AND_BAIL;
    }
}

#define eUnityPrintPointlessAndBail()       \
{                                          \
    eUnityTestResultsFailBegin(lineNumber); \
    eUnityPrint(eUnityStrPointless);         \
    eUnityAddMsgIfSpecified(msg);           \
    EUNITY_FAIL_AND_BAIL; }
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
